pe1mew/NTRIP-Client-for-ESP32/NTRIPClient_Hardware/Prototype_AtomLite/Documentation/QS-1205CBUL-3A_front.jpg

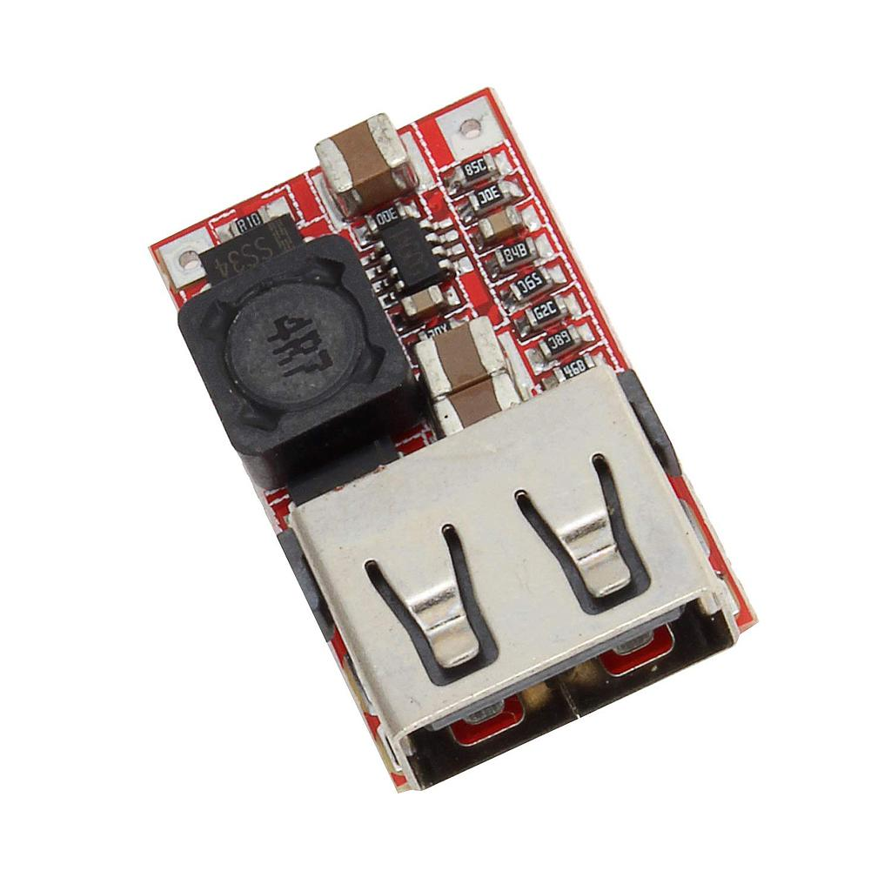
NTRIPClient_Hardware/Prototype_AtomLite/Documentation/QS-1205CBUL-3A_front.jpg
