pe1mew/NTRIP-Client-for-ESP32/NTRIPClient_Software/NTRIPClient_Documentation/images/NTRIPClient ActivityDiagram_plantuml.png

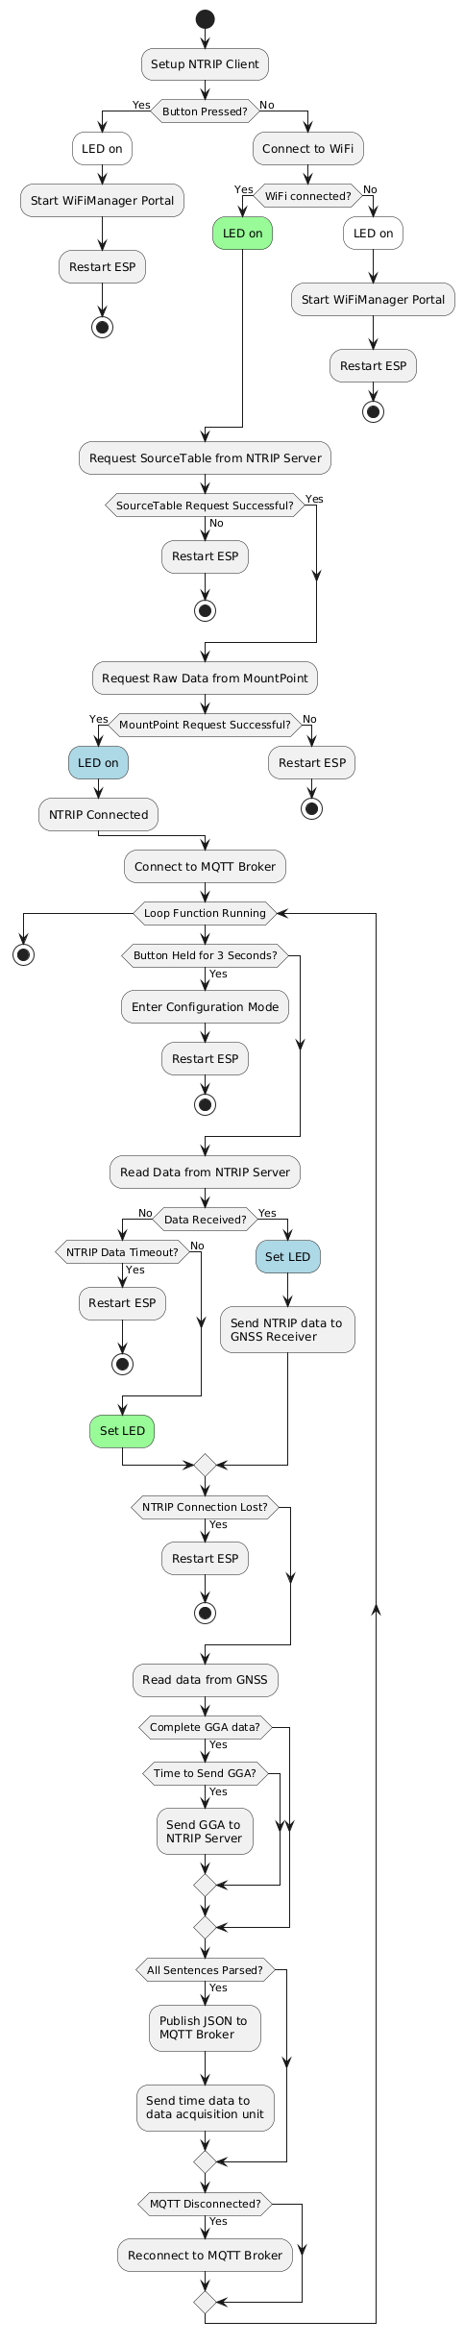
NTRIPClient_Software/NTRIPClient_Documentation/images/NTRIPClient ActivityDiagram_plantuml.png
