pe1mew/NTRIP-Client-for-ESP32/NTRIPClient_Software/NTRIPClient_WemosS3_ESP32-S3/SDS00001.png

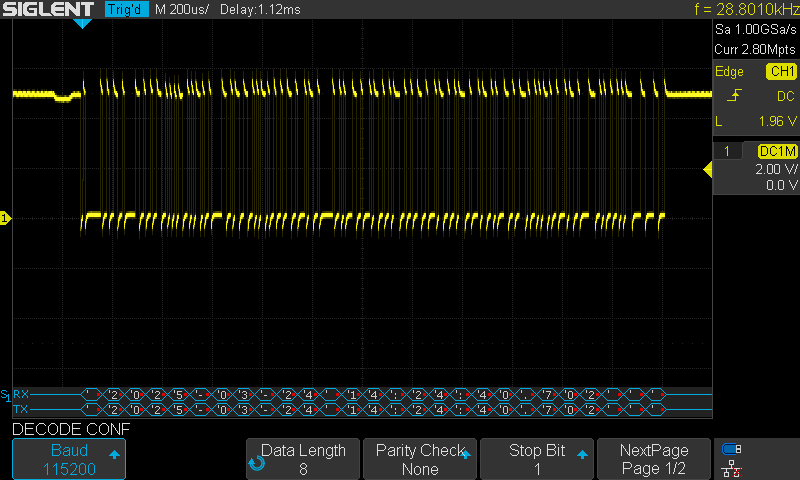
NTRIPClient_Software/NTRIPClient_WemosS3_ESP32-S3/SDS00001.png
